jeroenvdw/wakeuplight/WakeUpLight/Literals_EN.h

/************************
 ** Literals.h (English version)
 ************************/

#ifndef ALARMLITERALH
#define ALARMLITERALH

#include"Arduino.h"

namespace AlarmLiterals {
  
  static const char ON[]       = "On ";
  static const char OFF[]      = "Off";
  static const char MIN[]      = "min"; //minutes
  static const char SEC[]      = "sec"; //seconds
  static const char TOMORROW[] = "Tomorrow";
  static const char MONDAY[]   = "Monday";
  static const char TUESDAY[]  = "Tuesday";
  static const char WEDNESDAY[] = "Wednesday";
  static const char THURSDAY[] = "Thursday";
  static const char FRIDAY[]   = "Friday";
  static const char SATURDAY[] = "Saturday";
  static const char SUNDAY[]   = "Sunday";
  static const char MENU[]     = "Menu";
  static const char ALARM[]    = "Alarm";
  static const char TIJD[]     = "Time";
  static const char INST[]     = "Settings";
  static const char UUR[]      = "Hour";
  static const char DAG[]      = "Day";
  static const char WUDUR[]    = "WakeUp-dur.";
  static const char WULUM[]    = "Max light";
  static const char WAKEUP[]   = "Wake Up!";
  static const char AL_OFF[]   = "Disable alarm?";
  static const char OK[]       = "OK";
  static const char ALARM1[]   = "First alarm";
  static const char ALARM2[]   = "Second alarm";
  static const char NONE[]     = "None";
  static const char SNDUR[]    = "Snooze dur.";
  static const char BLDUR[]    = "Backlight";
  static const char SND[]      = "Sound";
  static const char MEL[]      = "Melody";
  static const char AL_VOL[]   = "Alarm Vol.";
  static const char SN_VOL[]   = "Snooze Vol.";
  static const char BUZZER[]   = "Buzzer";
  static const char SN_ADV[]   = "Snooze Adver"; 

  
};

#endif
