jeroenvdw/wakeuplight/WakeUpLight/Literals.h

/************************
 ** Literals.h (Dutch version)
 ************************/

#ifndef ALARMLITERALH
#define ALARMLITERALH

#include"Arduino.h"

namespace AlarmLiterals {
  
  static const char ON[]       = "Aan";
  static const char OFF[]      = "Uit";
  static const char MIN[]      = "min"; //minutes
  static const char SEC[]      = "sec"; //seconds
  static const char TOMORROW[] = "Morgen";
  static const char MONDAY[]   = "Maandag";
  static const char TUESDAY[]  = "Dinsdag";
  static const char WEDNESDAY[] = "Woensdag";
  static const char THURSDAY[] = "Donderdag";
  static const char FRIDAY[]   = "Vrijdag";
  static const char SATURDAY[] = "Zaterdag";
  static const char SUNDAY[]   = "Zondag";
  static const char MENU[]     = "Menu";
  static const char ALARM[]    = "Alarm";
  static const char TIJD[]     = "Tijd";
  static const char INST[]     = "Instellingen";
  static const char UUR[]      = "Uur";
  static const char DAG[]      = "Dag";
  static const char WUDUR[]    = "WakeUp-duur";
  static const char WULUM[]    = "Max lichtst";
  static const char WAKEUP[]   = "Opstaan!";
  static const char AL_OFF[]   = "Alarm uitsch.?";
  static const char OK[]       = "OK";
  static const char ALARM1[]   = "Eerste alarm";
  static const char ALARM2[]   = "Tweede alarm";
  static const char NONE[]     = "Geen";
  static const char SNDUR[]    = "Snoozeduur";
  static const char BLDUR[]    = "Backlight";
  static const char SND[]      = "Geluid";
  static const char MEL[]      = "Melodie";
  static const char AL_VOL[]   = "Alarm Vol.";
  static const char SN_VOL[]   = "Snooze Vol.";
  static const char BUZZER[]   = "Buzzer";
  static const char SN_ADV[]   = "Snooze Adver"; 

  
};

#endif
